knivd/Base18/cards/rtc/electronics/Assembly Drawings.pdf

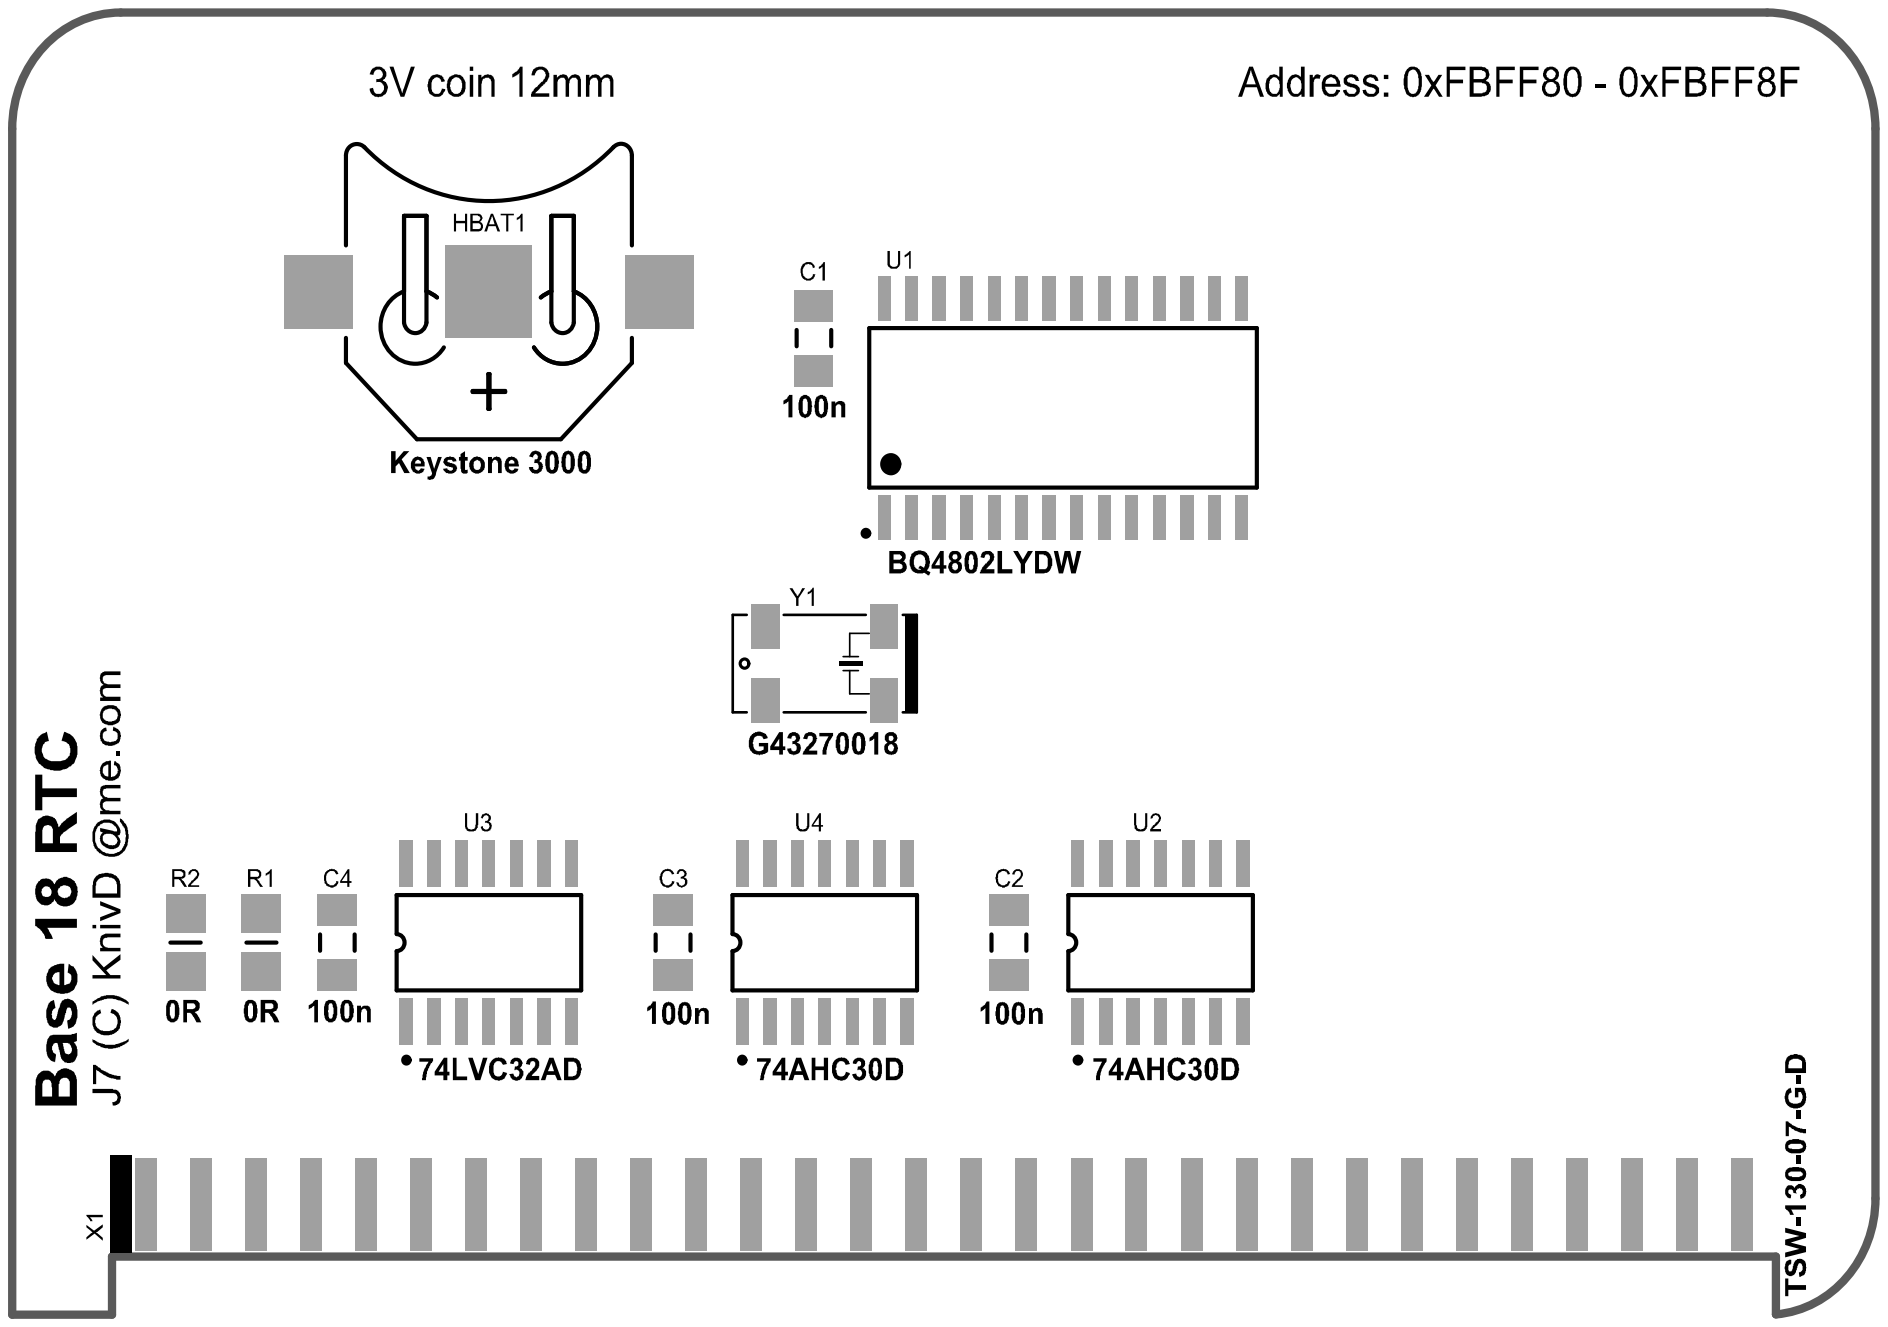
[picture p14: page 1]
