knivd/Base18/cards/rtc/electronics/Base18 RTC.pdf

# A20 INT0#

# INT2# RESET#

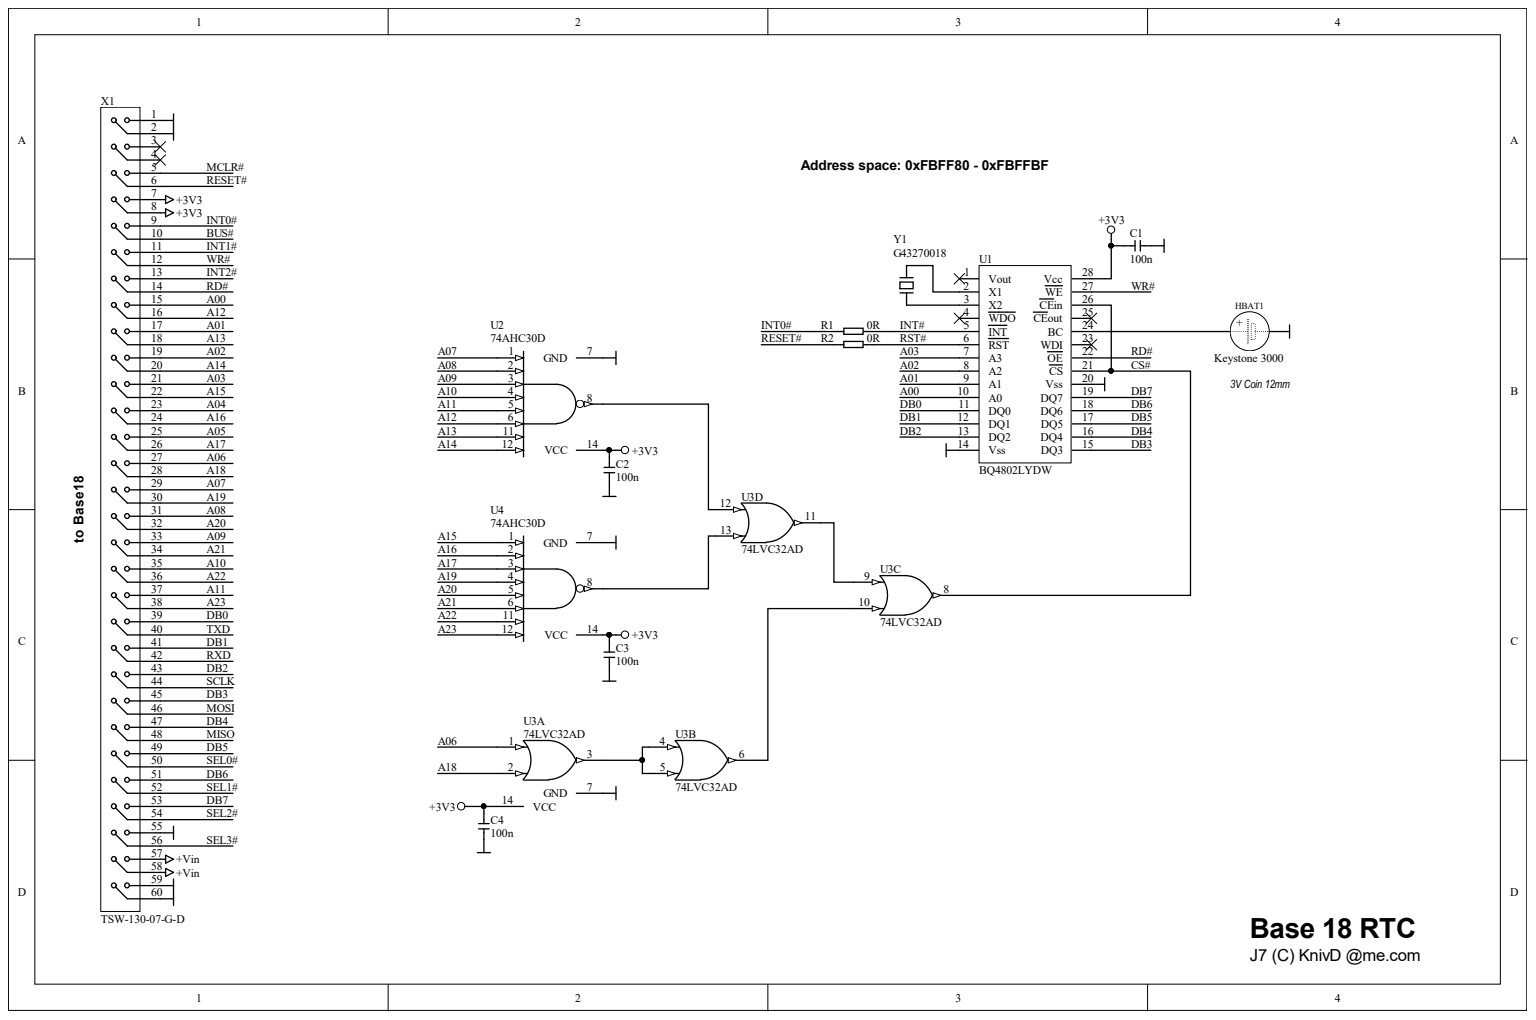
[picture p15: page 1]
