knivd/Base18/cards/sd/electronics/Assembly Drawings.pdf

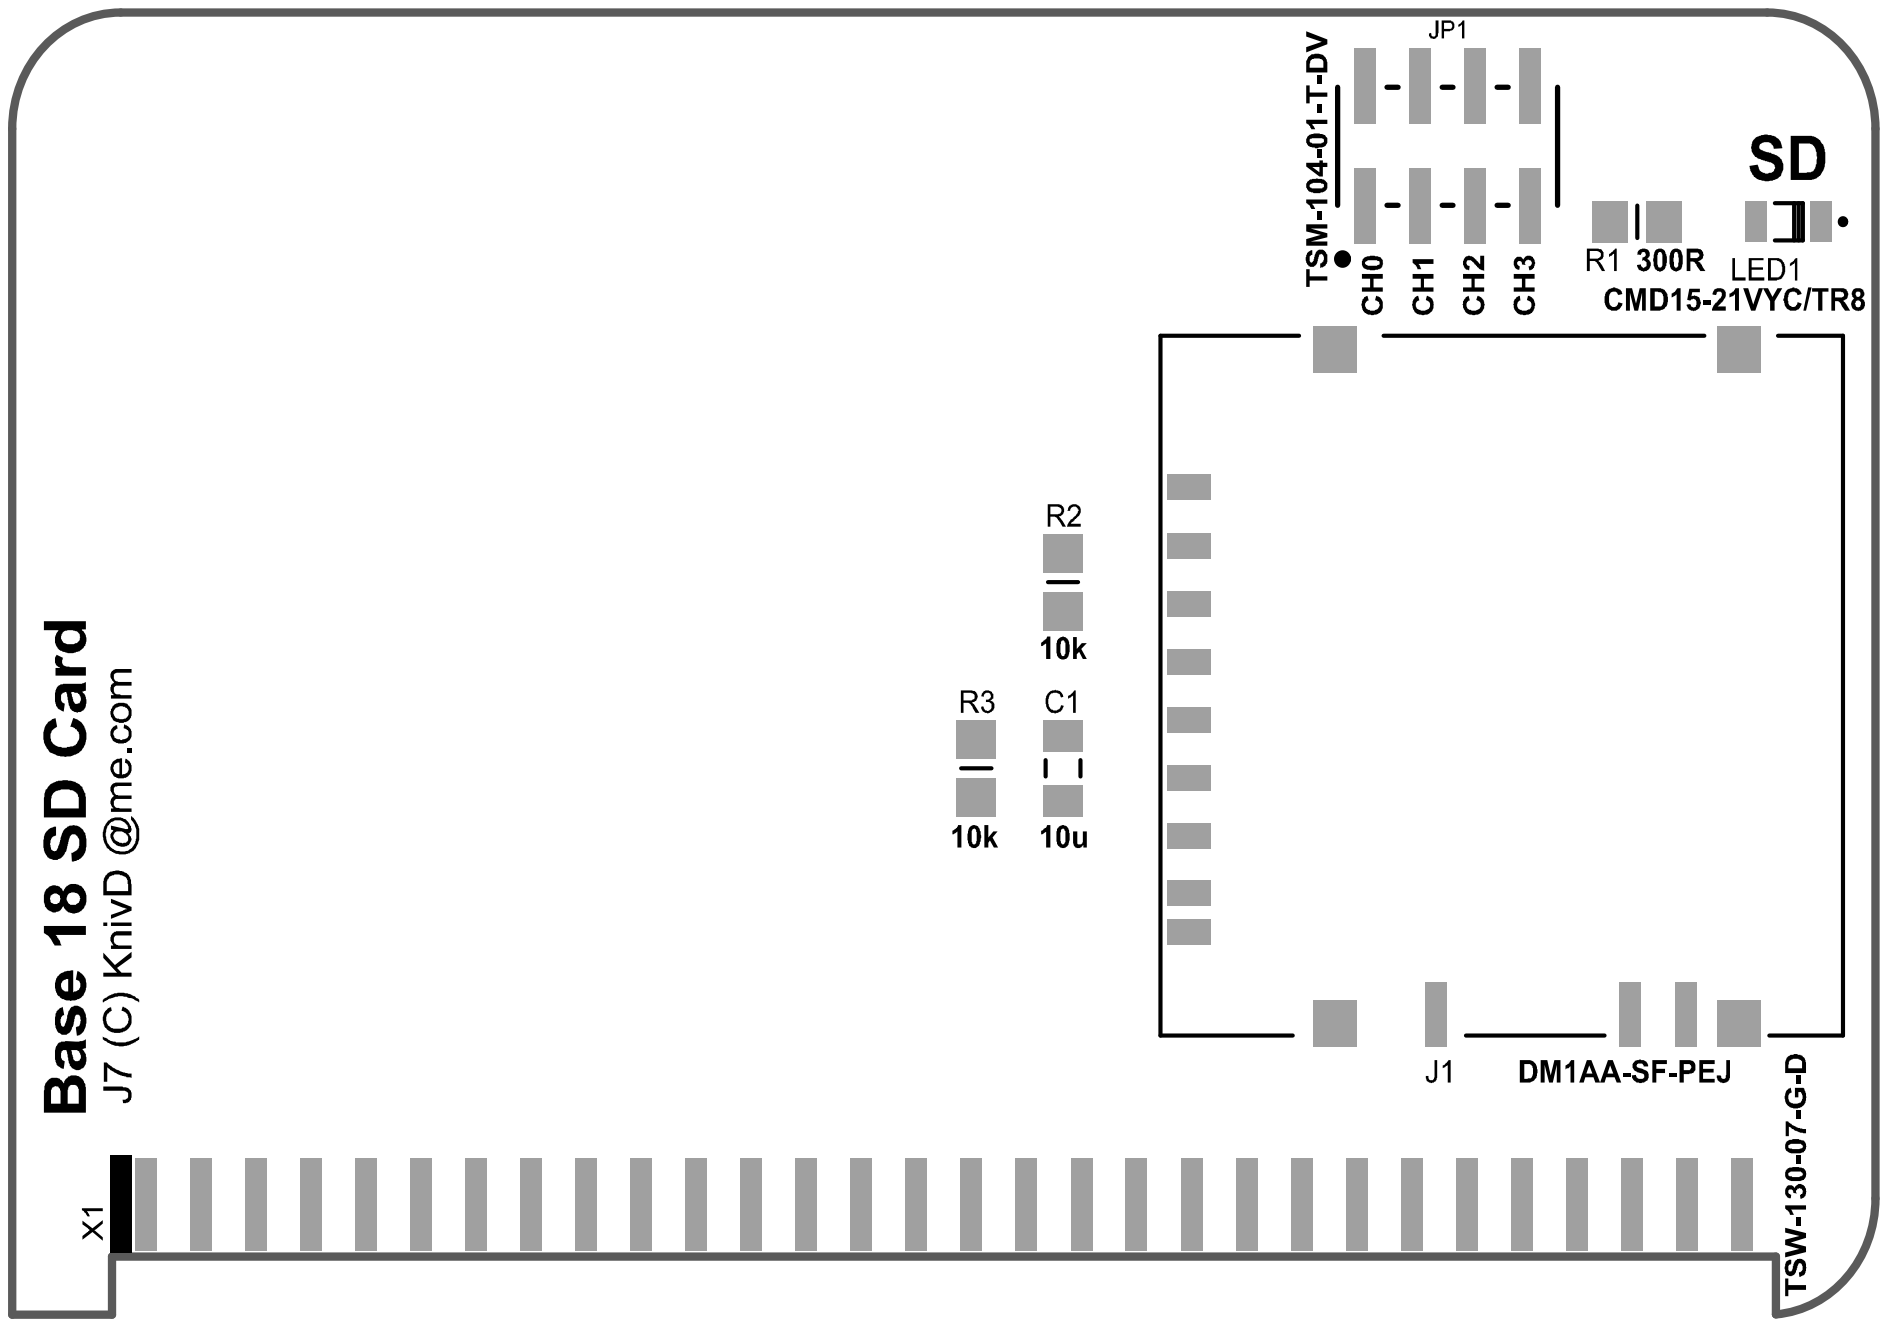
[picture p16: page 1]
