knivd/Base18/cards/sd/electronics/Base18 SD Card.pdf

# A20 INT0#

# INT2# RESET#

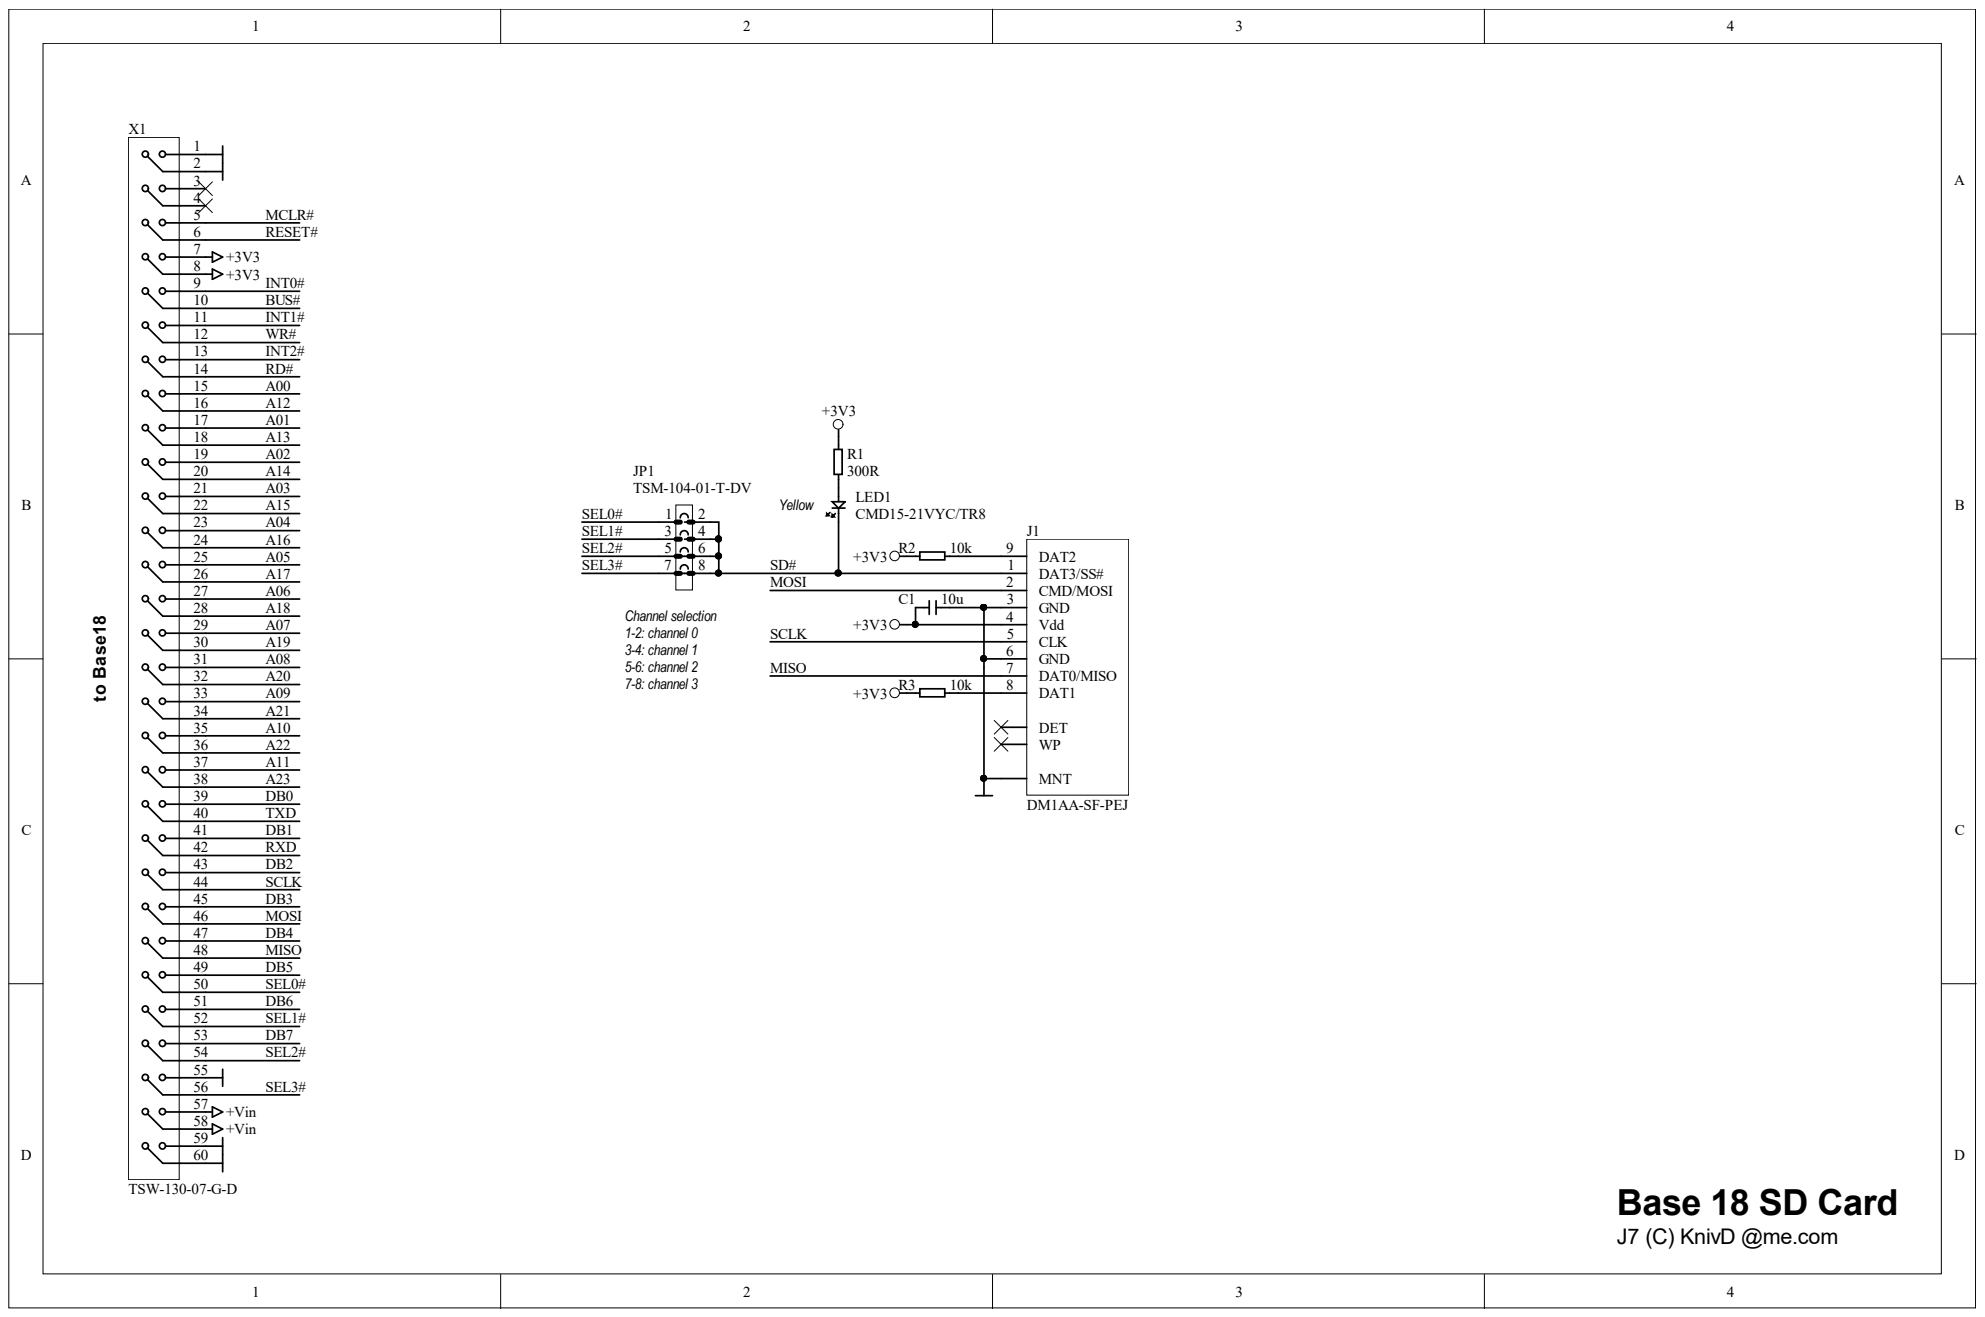
[picture p17: page 1]

Channel selection 1-2: channel 0 3-4: channel 1 5-6: channel 2 7-8: channel 3
